michael0093/RainSensor/LTSpice/Opamp-AC.asc

C1: cap; 1n
C2: cap; 100p
C3: cap; {Cf}
D1: schottky; BAT54SHY
D2: schottky; BAT54SHY
R1: res; 500k
R2: res; 100k
R3: res; 10k
R4: res; 10k
R5: res; 10Meg
U1: ADA4666-2
V1: voltage; AC 1
V2: voltage; 5
Named nets: 0
.ac dec 100 1 1meg
.step param Cf list 10p 1n 10n 100n 220n
