michael0093/RainSensor/LTSpice/Opamp-AC2.asc

C1: cap; 1n
C2: cap; 100p
C3: cap; {Cf}
C4: cap; 33n
D1: schottky; BAT54SHY
D2: schottky; BAT54SHY
R1: res; 250k
R2: res; 100k
R3: res; 10k
R4: res; 10k
R5: res; 10Meg
R6: res; 0
U1: LMX24_LM2902
V1: voltage; AC 1
V2: voltage; 5V
Named nets: 0
.ac dec 100 1 1meg
.step param Cf list 10p 1n 10n 100n 220n 470n
.step param Rf list 500k 300k 100k 10k
.step param CL list 22n 33n 47n 56n 68n 82n 100n
