michael0093/RainSensor/LTSpice/RainSensor.asc

C1: cap; 100n; IC=0
C2: cap; 100n
C3: cap; 100n
C4: cap; {Cf}
C5: cap; 1n
C6: cap; 100p
C7: cap; 60p
C8: cap; 22p
D1: schottky; BAT54SHY
D2: schottky; BAT54SHY
D3: diode; 1N4148
R1: res; 1k
R2: res; 10k
R3: res; 10k
R4: res; 10k
R5: res; 1k
R6: res; 7k5
R7: res; 100k
R8: res; 400k
R9: res; 10k
R10: res; 100k
R11: res; 10k
R12: res; 900
R13: res; 1Meg
R14: res; 1Meg
R15: res; 20Meg
R16: res; 10k
U1: ADA4666-2
U2: ADA4666-2
U3: ADA4666-2
U4: ADA4666-2
V1: voltage; 5
Named nets: 0, DigitalOut, AnalogOut
.tran 0 70m 50m
.step param C list 60p 90p
.step param Cf list 10p 1n 100n
